TheSuperPixel/7x7x7_cube_robot/cube_robot_7x7x7-master/cube_robot_kernel_module/step_tab.h

// 初始速度：1000.00 steps/s
// 最大速度：6000.00 steps/s
// 加速度：50000.00 steps/s2
// 加速距离：350.00 steps
int m3_length = 350;
int m3_array[350] = {
    477, 456, 439, 423, 408, 395, 383, 373, 363, 354, 345, 337, 330, 323, 316, 310, 
    304, 299, 294, 289, 284, 280, 275, 271, 267, 264, 260, 256, 253, 250, 247, 244, 
    241, 238, 236, 233, 231, 228, 226, 224, 221, 219, 217, 215, 213, 211, 209, 208, 
    206, 204, 202, 201, 199, 198, 196, 195, 193, 192, 190, 189, 188, 186, 185, 184, 
    183, 181, 180, 179, 178, 177, 176, 175, 174, 173, 171, 170, 170, 169, 168, 167, 
    166, 165, 164, 163, 162, 161, 161, 160, 159, 158, 157, 157, 156, 155, 154, 154, 
    153, 152, 151, 151, 150, 149, 149, 148, 147, 147, 146, 146, 145, 144, 144, 143, 
    143, 142, 141, 141, 140, 140, 139, 139, 138, 138, 137, 137, 136, 136, 135, 135, 
    134, 134, 133, 133, 132, 132, 131, 131, 130, 130, 130, 129, 129, 128, 128, 127, 
    127, 127, 126, 126, 125, 125, 125, 124, 124, 123, 123, 123, 122, 122, 122, 121, 
    121, 121, 120, 120, 120, 119, 119, 119, 118, 118, 118, 117, 117, 117, 116, 116, 
    116, 115, 115, 115, 114, 114, 114, 114, 113, 113, 113, 112, 112, 112, 112, 111, 
    111, 111, 110, 110, 110, 110, 109, 109, 109, 109, 108, 108, 108, 108, 107, 107, 
    107, 107, 106, 106, 106, 106, 105, 105, 105, 105, 104, 104, 104, 104, 104, 103, 
    103, 103, 103, 102, 102, 102, 102, 102, 101, 101, 101, 101, 101, 100, 100, 100, 
    100, 100,  99,  99,  99,  99,  99,  98,  98,  98,  98,  98,  97,  97,  97,  97, 
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
    147, 146, 146, 146, 146, 146, 146, 146, 145, 145, 145, 145, 145, 145, 145, 144, 
    144, 144, 144, 144, 144, 144, 143, 143, 143, 143, 143, 143, 143, 142, 142, 142, 
    142, 142, 142, 142, 141, 141, 141, 141, 141, 141, 141, 140, 140, 140, 140, 140, 
    140, 140, 140, 139, 139, 139, 139, 139, 139, 139, 139, 138, 138, 138, 138, 138, 
    138, 138, 138, 137, 137, 137, 137, 137, 137, 137, 137, 136, 136, 136, 136, 136, 
    136, 136, 136, 135, 135, 135, 135, 135, 135, 135, 135, 135, 134, 134, 134, 134, 
    134, 134, 134, 134, 133, 133, 133, 133, 133, 133, 133, 133, 133, 132, 132, 132, 
    132, 132, 132, 132, 132, 132, 131, 131, 131, 131, 131, 131, 131, 131, 131, 130, 
    130, 130, 130, 130, 130, 130, 130, 130, 130, 129, 129, 129, 129, 129, 129, 129, 
    129, 129, 129, 128, 128, 128, 128, 128, 128, 128, 128, 128, 128, 127, 127, 127, 
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
};
